giorossi91/livello_serbatoio/schemi/box/doc_componenti/push_button_dimension.jpg

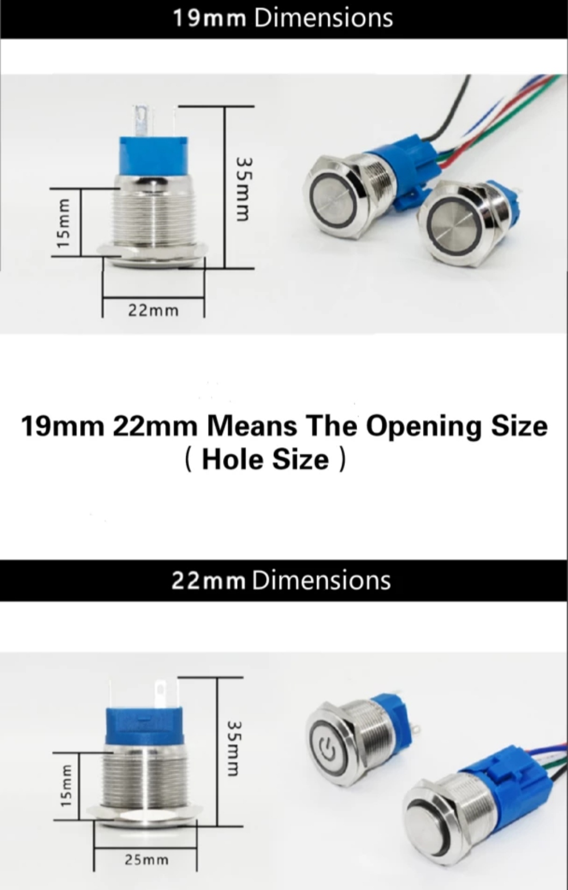
schemi/box/doc_componenti/push_button_dimension.jpg
