giorossi91/livello_serbatoio/schemi/box/senza_viti/img_senza_viti/box_bottom.png

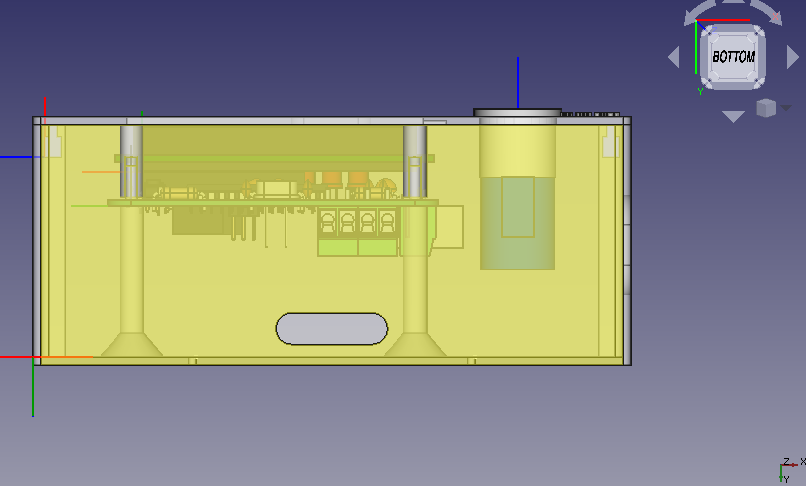
schemi/box/senza_viti/img_senza_viti/box_bottom.png
