giorossi91/livello_serbatoio/schemi/box/senza_viti/img_senza_viti/box_left.png

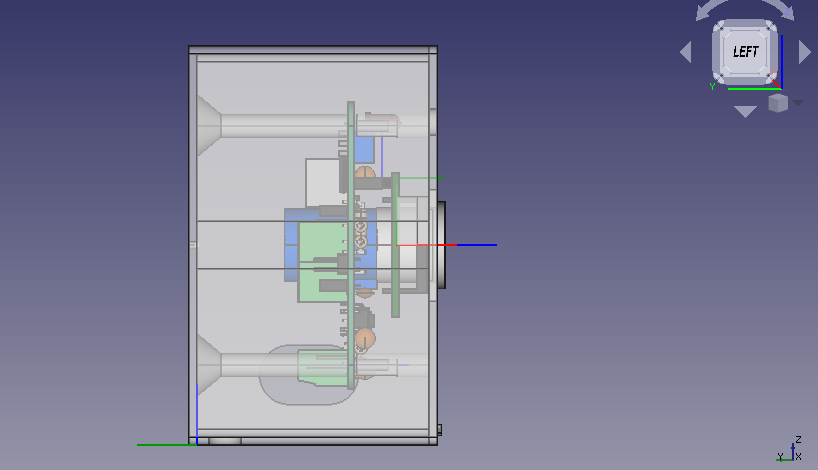
schemi/box/senza_viti/img_senza_viti/box_left.png
