giorossi91/livello_serbatoio/schemi/box/senza_viti/img_senza_viti/box_right.png

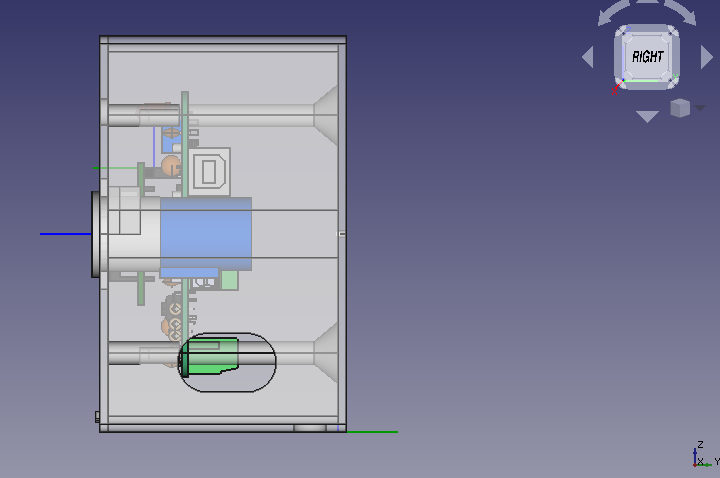
schemi/box/senza_viti/img_senza_viti/box_right.png
