giorossi91/livello_serbatoio/schemi/scheda_definitiva/immagini/box_bottom.png

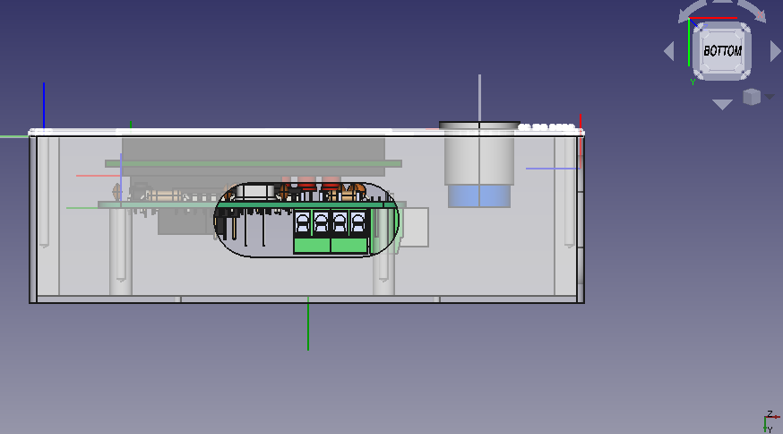
schemi/scheda_definitiva/immagini/box_bottom.png
