giorossi91/livello_serbatoio/schemi/scheda_definitiva/immagini/box_left.png

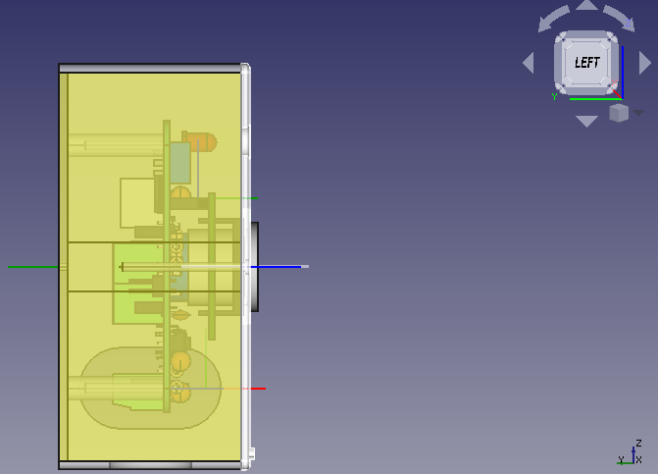
schemi/scheda_definitiva/immagini/box_left.png
