giorossi91/livello_serbatoio/schemi/scheda_definitiva/immagini/box_rear.png

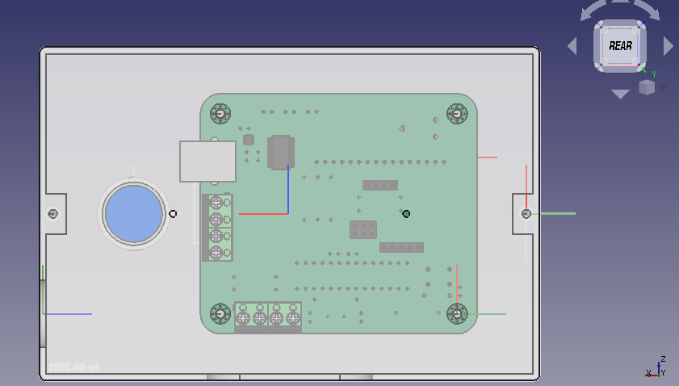
schemi/scheda_definitiva/immagini/box_rear.png
