giorossi91/livello_serbatoio/schemi/scheda_definitiva/immagini/box_right.png

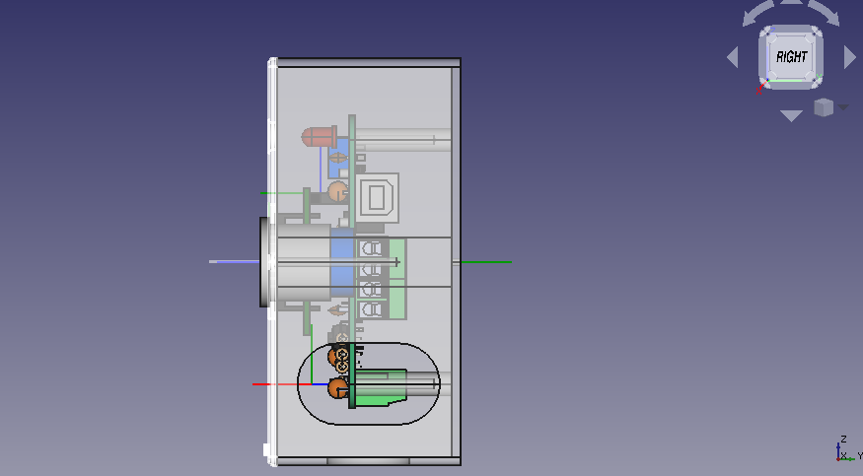
schemi/scheda_definitiva/immagini/box_right.png
