giorossi91/livello_serbatoio/schemi/scheda_definitiva/immagini/scheda_bottom.png

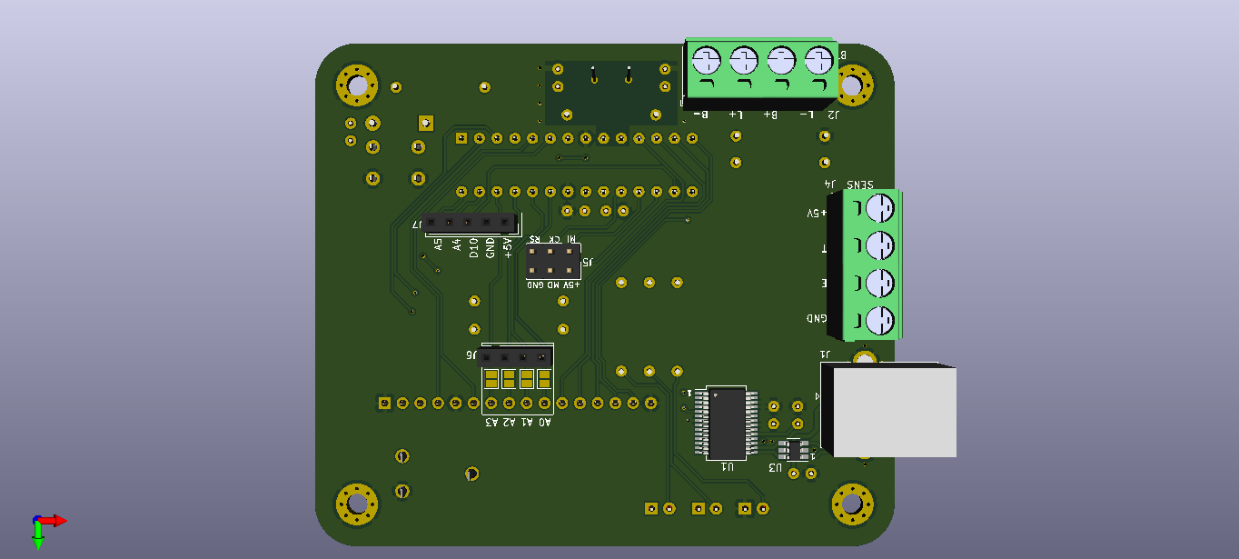
schemi/scheda_definitiva/immagini/scheda_bottom.png
