giorossi91/livello_serbatoio/schemi/scheda_definitiva/immagini/scheda_down.png

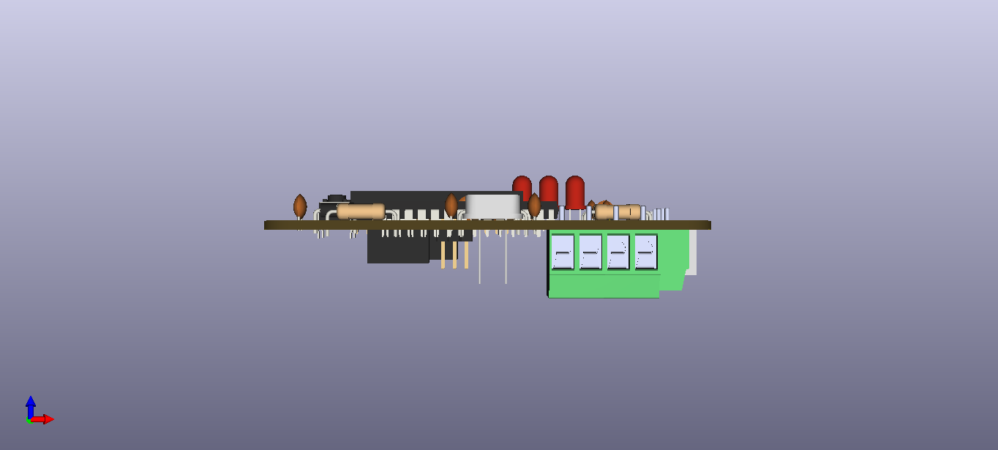
schemi/scheda_definitiva/immagini/scheda_down.png
