giorossi91/livello_serbatoio/schemi/box/senza_viti/coperchio_print.stl

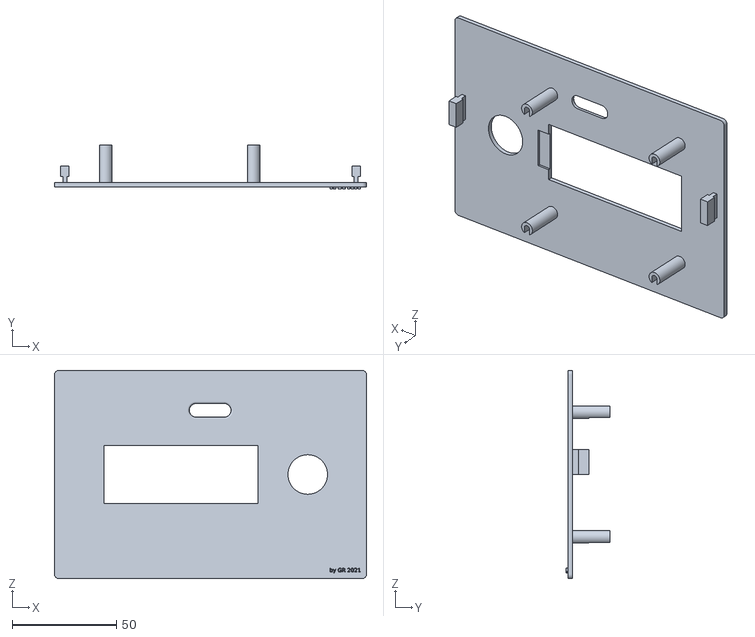
[picture p30: CAD file, 2020-12-20]
schemi/box/senza_viti/coperchio_print.stl
150.0 x 21.0 x 100.0
