giorossi91/livello_serbatoio/schemi/box/test_assembly_espansione/pcb_expansion.FCStd

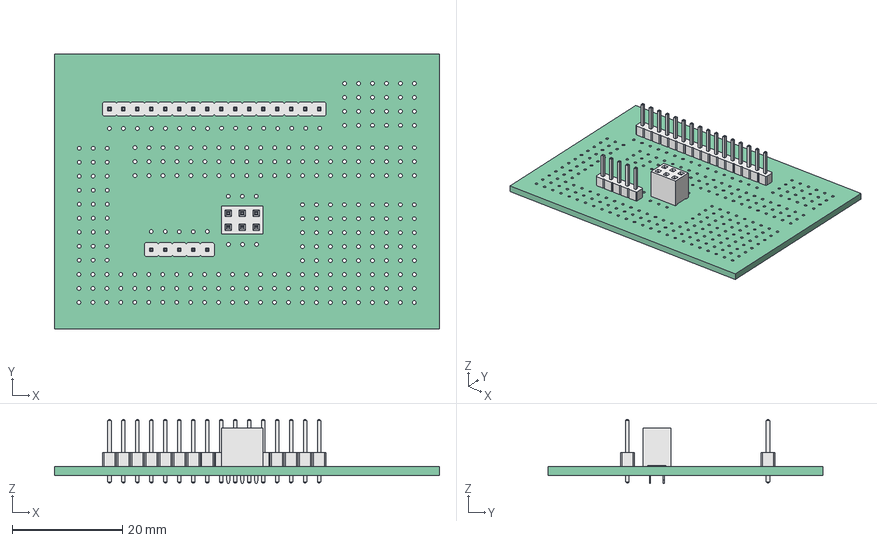
[picture p31: CAD file, 2020-12-30]
schemi/box/test_assembly_espansione/pcb_expansion.FCStd
70.0 x 50.0 x 11.6 mm
Pcb_d9e3
J2_PinSocket_2x03_P254mm_Vertical_5FEBA6ED
J3_PinHeader_1x16_P254mm_Vertical_5FEBA711
J1_PinHeader_1x05_P254mm_Vertical_5FEBBFE4
