giorossi91/livello_serbatoio/schemi/scheda_definitiva_ch340/3d_component/ACP470.step

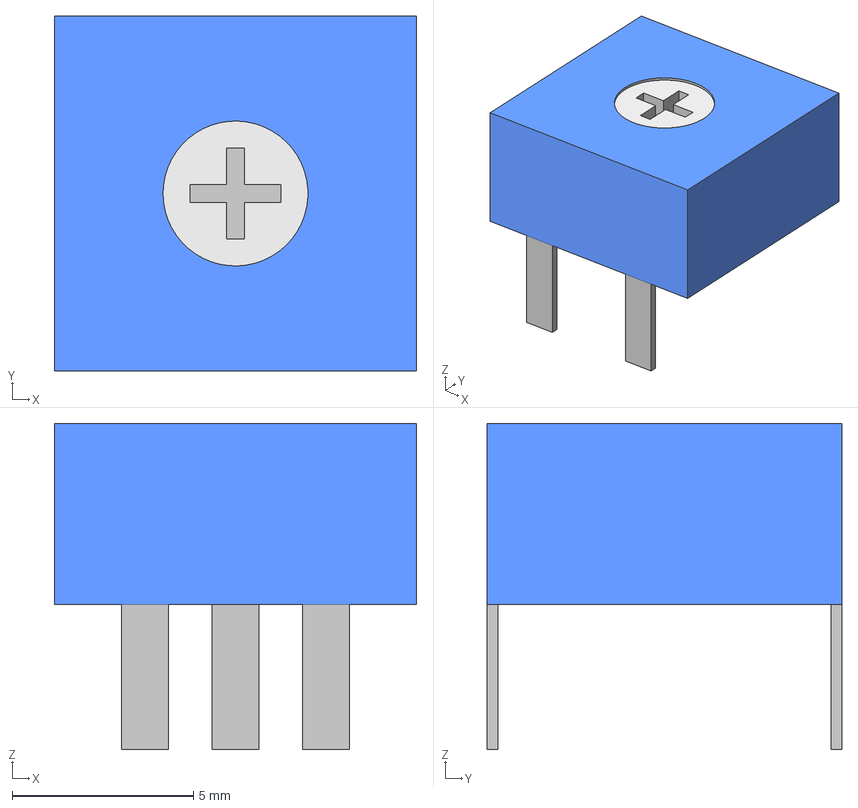
[picture p32: CAD file, 2020-11-15]
schemi/scheda_definitiva_ch340/3d_component/ACP470.step
10.0 x 9.80 x 9.00 mm
