giorossi91/livello_serbatoio/schemi/box/test_assembly_espansione/push_button.FCStd

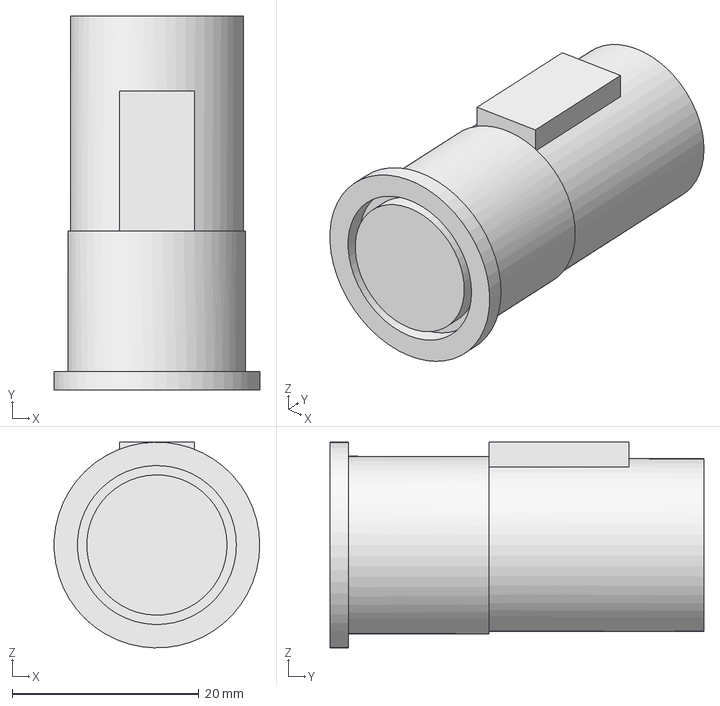
[picture p33: CAD file, 2020-12-30]
schemi/box/test_assembly_espansione/push_button.FCStd
22.0 x 40.0 x 22.0 mm
