giorossi91/livello_serbatoio/schemi/scheda_definitiva_ch340/3d_component/CUI_DEVICES_TB001-500-P04GR.step

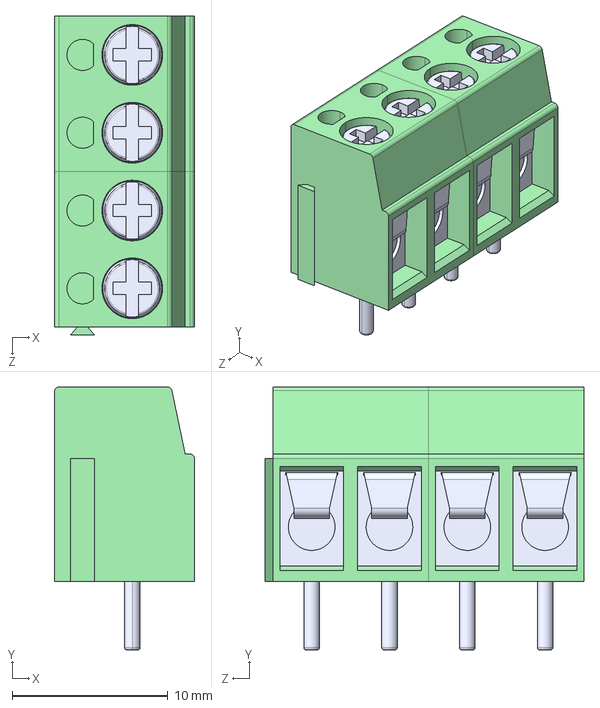
[picture p34: CAD file, 2020-11-15]
schemi/scheda_definitiva_ch340/3d_component/CUI_DEVICES_TB001-500-P04GR.step
9.00 x 16.9 x 20.5 mm
TB001-500-02P_Green - P x 2
