giorossi91/livello_serbatoio/schemi/scheda_definitiva_ch340/3d_component/usb_b_conn.step

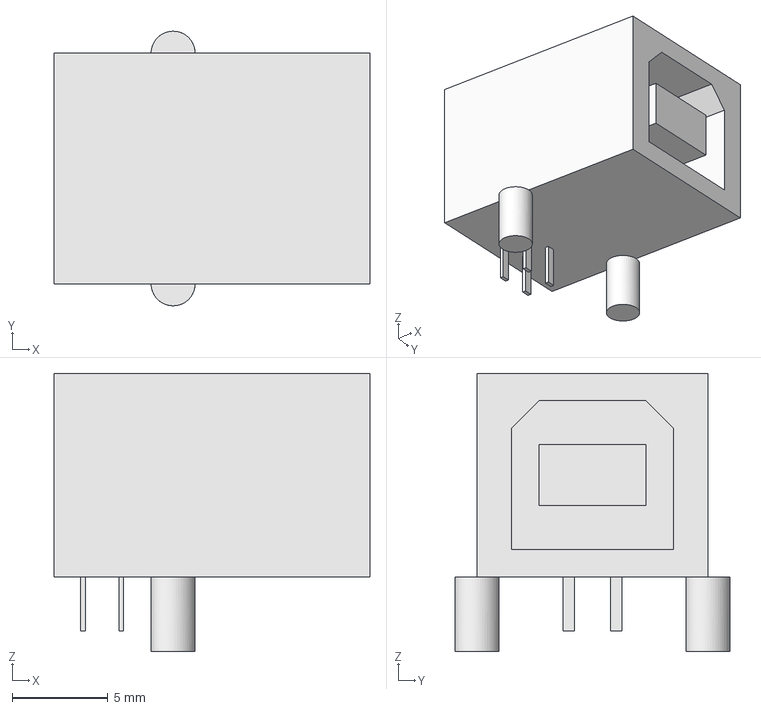
[picture p35: CAD file, 2020-10-18]
schemi/scheda_definitiva_ch340/3d_component/usb_b_conn.step
16.5 x 14.3 x 14.5 mm
