giorossi91/livello_serbatoio/schemi/scheda_definitiva_ch340/3d_component/usb_b_connector.FCStd

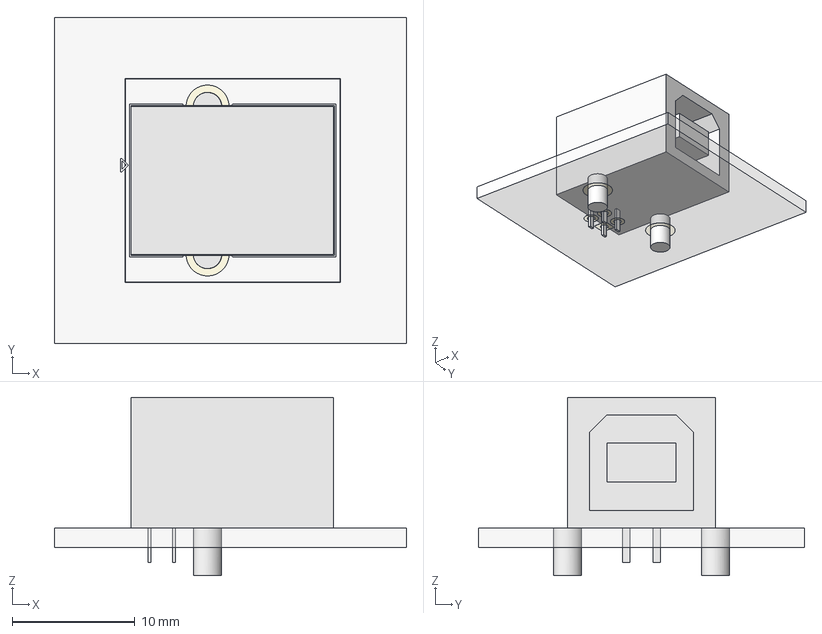
[picture p36: CAD file, 2020-10-18]
schemi/scheda_definitiva_ch340/3d_component/usb_b_connector.FCStd
28.7 x 26.5 x 14.5 mm
FCrtYd
FFab
FrontSilk
TopPads
BotPads
PTHs
Pcb
usb_b_conn
