giorossi91/livello_serbatoio/schemi/scheda_definitiva_ch340/3d_component/Crystal.step

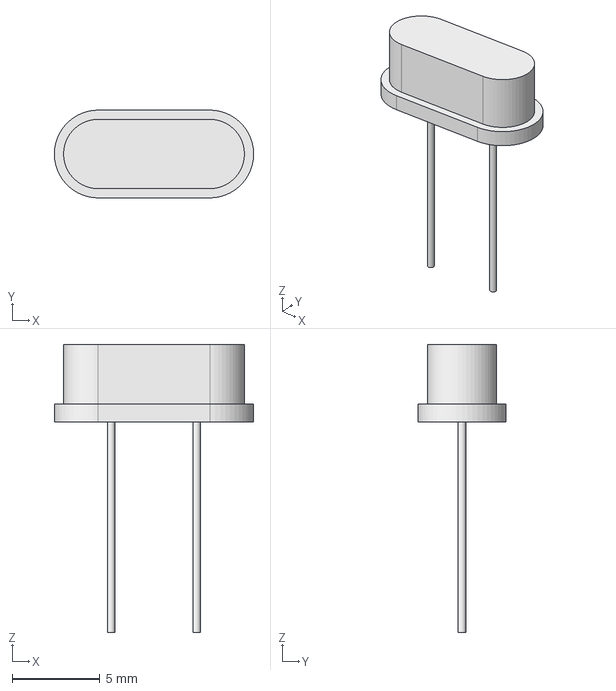
[picture p37: CAD file, 2020-08-20]
schemi/scheda_definitiva_ch340/3d_component/Crystal.step
11.3 x 5.00 x 16.4 mm
