giorossi91/livello_serbatoio/schemi/scheda_definitiva/doc_componenti/push_button_wiring.jpg

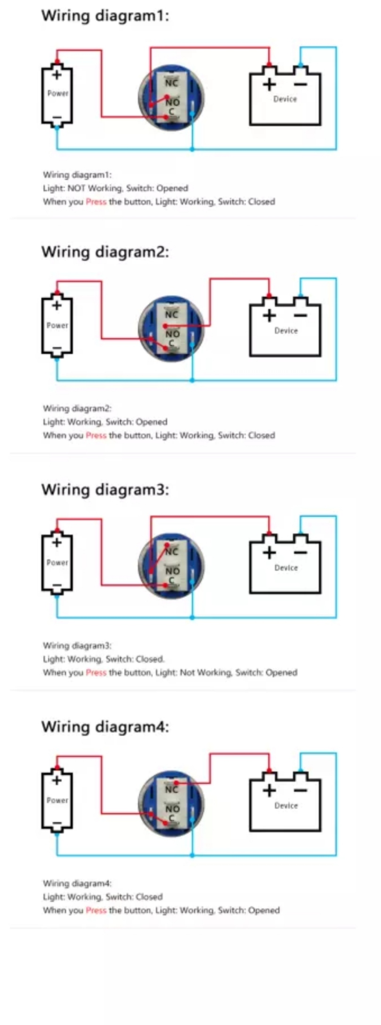
schemi/scheda_definitiva/doc_componenti/push_button_wiring.jpg
