giorossi91/livello_serbatoio/test/unit_test/livello_serbatoio_test.h

#ifndef LIVELLO_SERBATOIO_TEST_H_
#define LIVELLO_SERBATOIO_TEST_H_

#include <cppunit/extensions/HelperMacros.h>

#include <thread>
#include <atomic>
#include <cstdint>

namespace livelloSerbatoio_tests {

class LivelloSerbatoioTests  : public CppUnit::TestFixture {
  CPPUNIT_TEST_SUITE(LivelloSerbatoioTests);
  // === Unit tests ===
  CPPUNIT_TEST(test_PinSetup          );
  CPPUNIT_TEST(test_compute_liters    );
  CPPUNIT_TEST(test_compute_percentage);
  CPPUNIT_TEST(test_turn_on_lcd_light );
  CPPUNIT_TEST(test_turn_off_lcd_light);
  CPPUNIT_TEST(test_measure_level     );
  CPPUNIT_TEST(test_control_led       );
  CPPUNIT_TEST(test_sanitize_data     );
  CPPUNIT_TEST(test_update_lcd        );

  CPPUNIT_TEST(test_MedianFilter_init);
  CPPUNIT_TEST(test_MedianFilter_in  );
  CPPUNIT_TEST(test_MedianFilter_out );
  
  CPPUNIT_TEST(test_ConsumptionData_init             );
  CPPUNIT_TEST(test_ConsumptionData_updateTime       );
  CPPUNIT_TEST(test_ConsumptionData_updateConsumption);
  CPPUNIT_TEST(test_ConsumptionData_getConsumption1h );
  CPPUNIT_TEST(test_ConsumptionData_getConsumption12h);
  CPPUNIT_TEST(test_ConsumptionData_getConsumption1d );
  CPPUNIT_TEST(test_ConsumptionData_getConsumption3d );
  CPPUNIT_TEST(test_ConsumptionData_sumSamples       );
  CPPUNIT_TEST(test_ConsumptionData_updateBuffer     );
  CPPUNIT_TEST(test_ConsumptionData_updateIndex      );

  CPPUNIT_TEST(test_loop);
  CPPUNIT_TEST(test_loop_btn);
  // ==================
  CPPUNIT_TEST_SUITE_END();
  
public:
  void setUp   ( void ) override;
  void tearDown( void ) override;

protected:
  // === Unit tests ===
  void test_loop               ( void );
  void test_loop_btn           ( void );

  void test_compute_liters     ( void );
  void test_compute_percentage ( void );
  void test_PinSetup           ( void );
  void test_turn_on_lcd_light  ( void );
  void test_turn_off_lcd_light ( void );
  void test_measure_level      ( void );
  void test_control_led        ( void );
  void test_sanitize_data      ( void );
  void test_update_lcd         ( void );
  
  void test_MedianFilter_init  ( void );
  void test_MedianFilter_in    ( void );
  void test_MedianFilter_out   ( void );
  
  void test_ConsumptionData_init              ( void );
  void test_ConsumptionData_updateTime        ( void );
  void test_ConsumptionData_updateConsumption ( void );
  void test_ConsumptionData_getConsumption1h  ( void );
  void test_ConsumptionData_getConsumption12h ( void );
  void test_ConsumptionData_getConsumption1d  ( void );
  void test_ConsumptionData_getConsumption3d  ( void );
  void test_ConsumptionData_sumSamples        ( void );
  void test_ConsumptionData_updateBuffer      ( void );
  void test_ConsumptionData_updateIndex       ( void );
  
  // ==================

private:
  static const uint32_t TIME_STEP_MS;
  
  std::atomic<bool> time_on;
  std::thread       time_thread;

  uint32_t cycle_num;
  
  void timesim_thread ( void );
  
  void start_time ( void );
  void stop_time  ( void );

  void loopNTimes ( uint32_t n );

  static double expected_liters (const double d);

  [[noreturn]] static void printFail ( const char * str );
};

}

#endif // LIVELLO_SERBATOIO_TEST_H_
